abonham/BKM-10Replacements/BKM-10Rp2040/src/defaults.h

#ifndef DEFAULTS_H
#ifdef ONKYO
const char *defaultKeys = "[{\"id\":0,\"address\":27858,\"code\":203},{\"id\":1,\"address\":6610,\"code\":192},{\"id\":2,\"address\":28114,\"code\":151},{\"id\":3,\"address\":28114,\"code\":130},{\"id\":4,\"address\":28114,\"code\":131},{\"id\":5,\"address\":722,\"code\":222},{\"id\":6,\"address\":722,\"code\":213},{\"id\":7,\"address\":722,\"code\":214},{\"id\":8,\"address\":722,\"code\":215},{\"id\":9,\"address\":722,\"code\":216},{\"id\":10,\"address\":722,\"code\":217},{\"id\":11,\"address\":722,\"code\":218},{\"id\":12,\"address\":722,\"code\":219},{\"id\":13,\"address\":722,\"code\":220},{\"id\":14,\"address\":722,\"code\":221},{\"id\":15,\"address\":28114,\"code\":93},{\"id\":16,\"address\":28114,\"code\":149},{\"id\":17,\"address\":27858,\"code\":136},{\"id\":18,\"address\":28114,\"code\":2},{\"id\":19,\"address\":722,\"code\":144},{\"id\":20,\"address\":722,\"code\":143},{\"id\":21,\"address\":722,\"code\":129},{\"id\":22,\"address\":722,\"code\":141},{\"id\":23,\"address\":722,\"code\":128},{\"id\":24,\"address\":722,\"code\":145},{\"id\":25,\"address\":722,\"code\":142},{\"id\":26,\"address\":28114,\"code\":3},{\"id\":27,\"address\":44242,\"code\":208},{\"id\":28,\"address\":44242,\"code\":209},{\"id\":29,\"address\":44242,\"code\":210},{\"id\":30,\"address\":27858,\"code\":78},{\"id\":31,\"address\":28114,\"code\":5},{\"id\":32,\"address\":6610,\"code\":135},{\"id\":33,\"address\":6610,\"code\":130},{\"id\":34,\"address\":6610,\"code\":131}][{\"id\":0,\"address\":27858,\"code\":203},{\"id\":1,\"address\":6610,\"code\":192},{\"id\":2,\"address\":28114,\"code\":151},{\"id\":3,\"address\":28114,\"code\":130},{\"id\":4,\"address\":28114,\"code\":131},{\"id\":5,\"address\":722,\"code\":222},{\"id\":6,\"address\":722,\"code\":213},{\"id\":7,\"address\":722,\"code\":214},{\"id\":8,\"address\":722,\"code\":215},{\"id\":9,\"address\":722,\"code\":216},{\"id\":10,\"address\":722,\"code\":217},{\"id\":11,\"address\":722,\"code\":218},{\"id\":12,\"address\":722,\"code\":219},{\"id\":13,\"address\":722,\"code\":220},{\"id\":14,\"address\":722,\"code\":221},{\"id\":15,\"address\":28114,\"code\":93},{\"id\":16,\"address\":28114,\"code\":149},{\"id\":17,\"address\":27858,\"code\":136},{\"id\":18,\"address\":28114,\"code\":2},{\"id\":19,\"address\":722,\"code\":144},{\"id\":20,\"address\":722,\"code\":143},{\"id\":21,\"address\":722,\"code\":129},{\"id\":22,\"address\":722,\"code\":141},{\"id\":23,\"address\":722,\"code\":128},{\"id\":24,\"address\":722,\"code\":145},{\"id\":25,\"address\":722,\"code\":142},{\"id\":26,\"address\":28114,\"code\":3},{\"id\":27,\"address\":44242,\"code\":208},{\"id\":28,\"address\":44242,\"code\":209},{\"id\":29,\"address\":44242,\"code\":210},{\"id\":30,\"address\":27858,\"code\":78},{\"id\":31,\"address\":28114,\"code\":5},{\"id\":32,\"address\":6610,\"code\":135},{\"id\":33,\"address\":6610,\"code\":130},{\"id\":34,\"address\":6610,\"code\":131}]";
#endif

#ifdef CVC707V
const char *defaultKeys = "[{\"id\":0,\"address\":1414,\"code\":15},{\"id\":1,\"address\":1414,\"code\":75},{\"id\":2,\"address\":1414,\"code\":24},{\"id\":3,\"address\":1414,\"code\":21},{\"id\":4,\"address\":1414,\"code\":22},{\"id\":5,\"address\":1414,\"code\":9},{\"id\":6,\"address\":1414,\"code\":0},{\"id\":7,\"address\":1414,\"code\":1},{\"id\":8,\"address\":1414,\"code\":2},{\"id\":9,\"address\":1414,\"code\":3},{\"id\":10,\"address\":1414,\"code\":4},{\"id\":11,\"address\":1414,\"code\":5},{\"id\":12,\"address\":1414,\"code\":6},{\"id\":13,\"address\":1414,\"code\":7},{\"id\":14,\"address\":1414,\"code\":8},{\"id\":15,\"address\":1414,\"code\":16},{\"id\":16,\"address\":1414,\"code\":28},{\"id\":17,\"address\":1414,\"code\":23},{\"id\":18,\"address\":1414,\"code\":76},{\"id\":19,\"address\":1414,\"code\":73},{\"id\":20,\"address\":1414,\"code\":18},{\"id\":21,\"address\":1414,\"code\":84},{\"id\":22,\"address\":1414,\"code\":85},{\"id\":23,\"address\":1414,\"code\":87},{\"id\":24,\"address\":1414,\"code\":78},{\"id\":25,\"address\":1414,\"code\":20},{\"id\":26,\"address\":1414,\"code\":88},{\"id\":27,\"address\":1414,\"code\":89},{\"id\":28,\"address\":1414,\"code\":27},{\"id\":29,\"address\":1414,\"code\":65},{\"id\":30,\"address\":1414,\"code\":86},{\"id\":31,\"address\":1414,\"code\":19},{\"id\":32,\"address\":1414,\"code\":17},{\"id\":33,\"address\":1414,\"code\":10},{\"id\":34,\"address\":1414,\"code\":11}]";
#endif
#endif
